cjm571/diyer-cutter/docs/KiCad/DIYer_Cutter/DIYer_Cutter.kicad_pcb

## KiCad design sch/Z80proto2/Comm_Module.kicad_sch

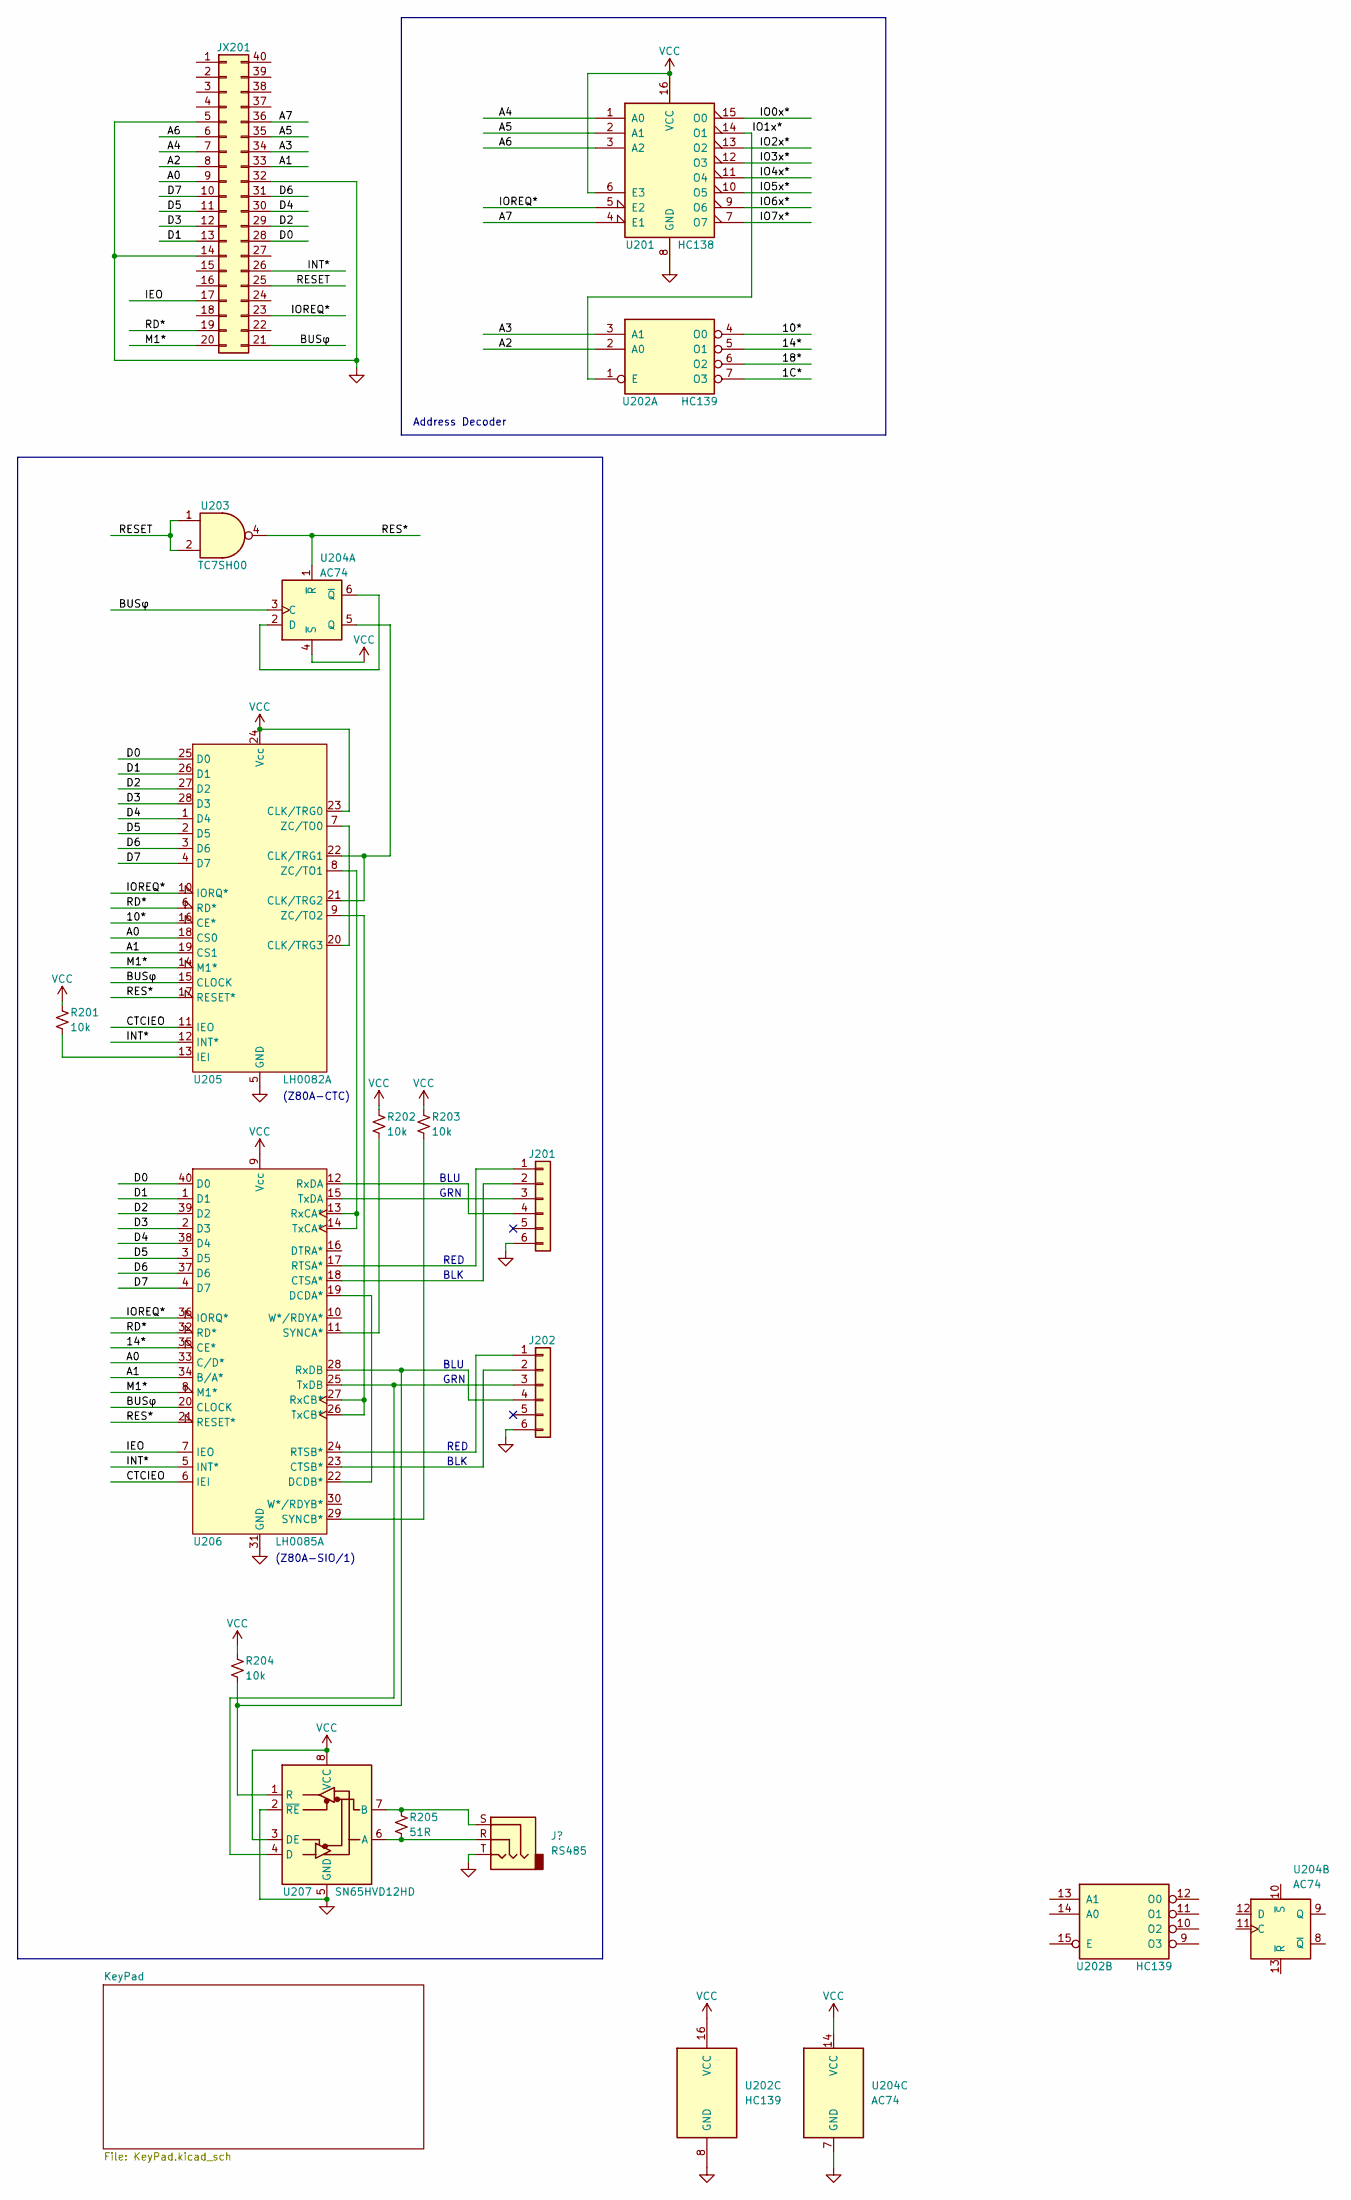
[picture p6: schematic Comm_Module.kicad_sch]

Parts:
J201, J202: Conn_01x06
JX201: Conn_02x20_Counter_Clockwise
R201, R202, R203, R204: 10k
R205: 51R
U201: HC138
U202: HC139
U203: TC7SH00
U204: AC74
U205: LH0082A
U206: LH0085A
U207: SN65HVD12HD; SOIC-8_3.9x4.9mm_P1.27mm

Connections:
1C*: U202.7 (O3)
10*: U202.4 (O0), U205.16 (CE*)
14*: U202.5 (O1), U206.35 (CE*)
18*: U202.6 (O2)
A0: JX201.9, U205.18 (CS0), U206.33 (C/D*)
A1: JX201.33, U205.19 (CS1), U206.34 (B/A*)
A2: JX201.8, U202.2 (A0)
A3: JX201.34, U202.3 (A1)
A4: JX201.7, U201.1 (A0)
A5: JX201.35, U201.2 (A1)
A6: JX201.6, U201.3 (A2)
A7: JX201.36, U201.4 (E1)
BUSφ: JX201.21, U204.3 (C), U205.15 (CLOCK), U206.20 (CLOCK)
CTCIEO: U205.11 (IEO), U206.6 (IEI)
D0: JX201.28, U205.25 (D0), U206.40 (D0)
D1: JX201.13, U205.26 (D1), U206.1 (D1)
D2: JX201.29, U205.27 (D2), U206.39 (D2)
D3: JX201.12, U205.28 (D3), U206.2 (D3)
D4: JX201.30, U205.1 (D4), U206.38 (D4)
D5: JX201.11, U205.2 (D5), U206.3 (D5)
D6: JX201.31, U205.3 (D6), U206.37 (D6)
D7: JX201.10, U205.4 (D7), U206.4 (D7)
IEO: JX201.17, U206.7 (IEO)
INT*: JX201.26, U205.12 (INT*), U206.5 (INT*)
IO0x*: U201.15 (O0)
IO1x*: U201.14 (O1), U202.1 (E)
IO2x*: U201.13 (O2)
IO3x*: U201.12 (O3)
IO4x*: U201.11 (O4)
IO5x*: U201.10 (O5)
IO6x*: U201.9 (O6)
IO7x*: U201.7 (O7)
IOREQ*: JX201.23, U201.5 (E2), U205.10 (IORQ*), U206.36 (IORQ*)
M1*: JX201.20, U205.14 (M1*), U206.8 (M1*)
unnamed: J201.1, U206.17 (RTSA*)
unnamed: J201.2, U206.18 (CTSA*)
unnamed: J201.3, U206.15 (TxDA)
unnamed: J201.4, U206.12 (RxDA)
unnamed: J202.1, U206.24 (RTSB*)
unnamed: J202.2, U206.23 (CTSB*)
unnamed: J202.3, U206.25 (TxDB), U207.4 (D)
unnamed: J202.4, R204.2, U206.28 (RxDB), U207.1 (R)
unnamed: JX201.5, JX201.14, JX201.32
unnamed: R201.2, U205.13 (IEI)
unnamed: R202.2, U206.11 (SYNCA*)
unnamed: R203.2, U206.29 (SYNCB*)
unnamed: R205.1, U207.7 (B)
unnamed: R205.2, U207.6 (A)
unnamed: U201.6 (E3), U201.16 (VCC)
unnamed: U204.2 (D), U204.6 (~Q)
unnamed: U204.5 (Q), U205.21 (CLK/TRG2), U205.22 (CLK/TRG1)
unnamed: U205.8 (ZC/TO1), U206.13 (RxCA*), U206.14 (TxCA*)
unnamed: U205.9 (ZC/TO2), U206.26 (TxCB*), U206.27 (RxCB*)
unnamed: U205.7 (ZC/TO0), U205.20 (CLK/TRG3)
unnamed: U205.23 (CLK/TRG0), U205.24 (Vcc)
unnamed: U206.19 (DCDA*), U206.22 (DCDB*)
unnamed: U207.2 (~RE), U207.5 (GND)
unnamed: U207.3 (DE), U207.8 (VCC)
RD*: JX201.19, U205.6 (RD*), U206.32 (RD*)
RES*: U203.4, U204.1 (~R), U205.17 (RESET*), U206.21 (RESET*)
RESET: JX201.25, U203.1, U203.2

Notes on the sheet:
BLK
RED
Address Decoder
(Z80A-CTC)
BLU
GRN
(Z80A-SIO/1)
