cjm571/diyer-cutter/docs/KiCad/DIYer_Cutter/DIYer_Cutter.kicad_pcb

## KiCad design sch/Z80proto2/KeyPad.kicad_sch

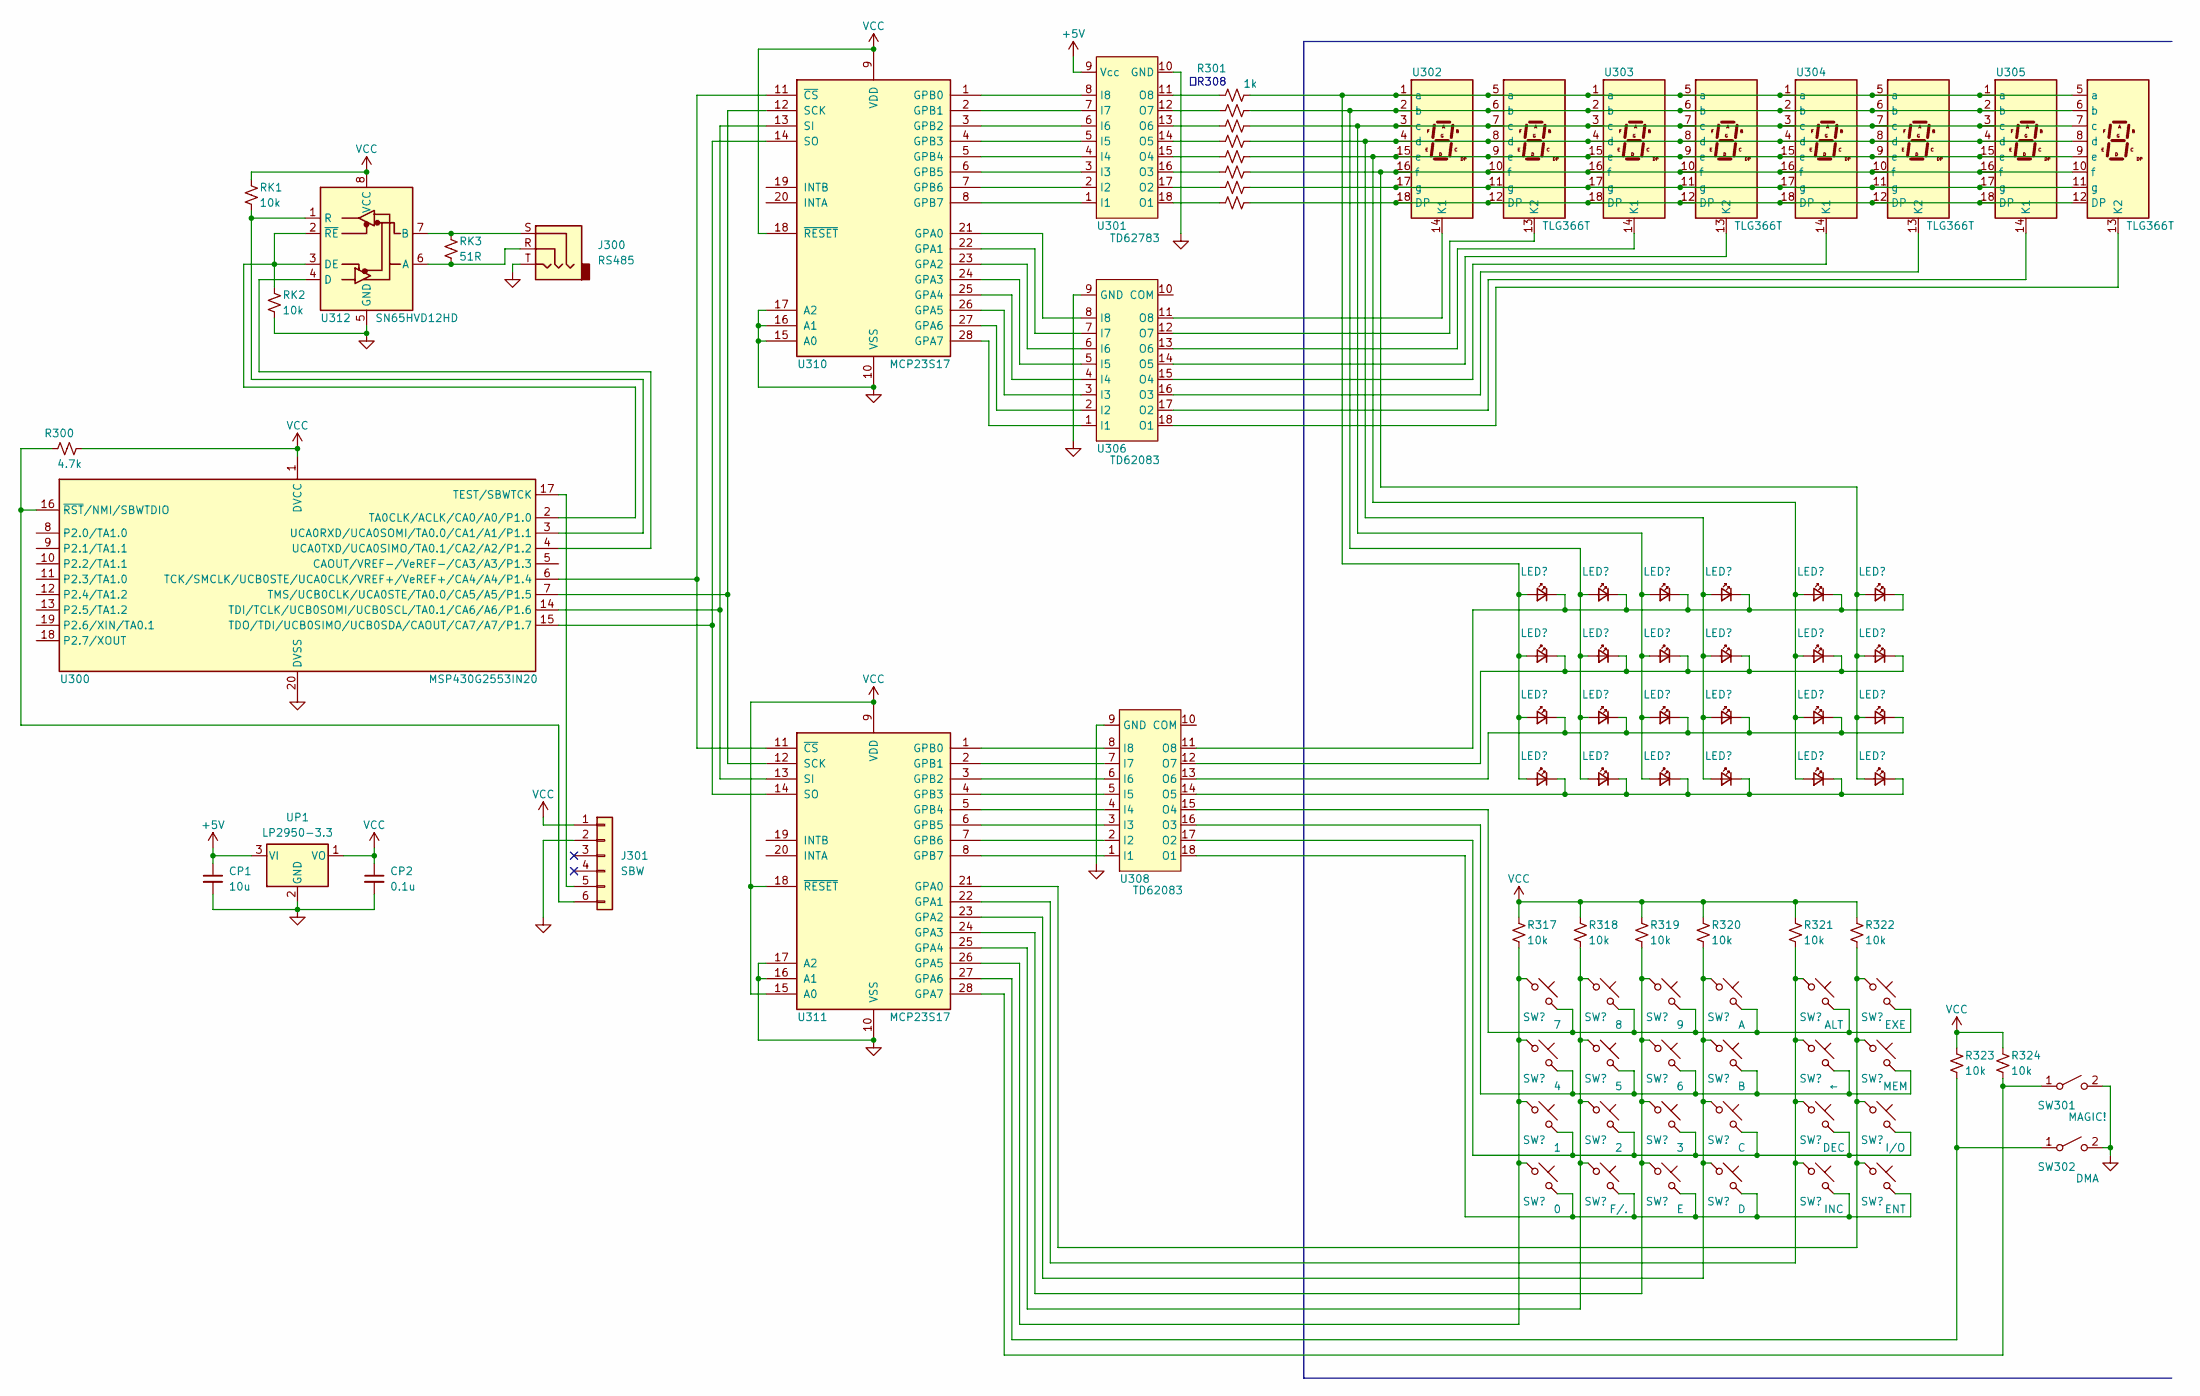
[picture p8: schematic KeyPad.kicad_sch]

Parts:
CP1: 10u
CP2: 0.1u
J300: RS485
J301: SBW
R300: 4.7k
R301, R302, R303, R304, R305, R306, R307, R308: 1k
R317, R318, R319, R320, R321, R322, R323, R324: 10k
RK1, RK2: 10k
RK3: 51R
SW301: MAGIC!
SW302: DMA
U300: MSP430G2553IN20; DIP-20_W7.62mm
U301: TD62783
U302, U303, U304, U305: TLG366T
U306, U308: TD62083
U310, U311: MCP23S17; DIP-28_W7.62mm
U312: SN65HVD12HD; SOIC-8_3.9x4.9mm_P1.27mm
UP1: LP2950-3.3; TO-92_Inline

Connections:
unnamed: CP1.1, UP1.3 (VI)
unnamed: CP1.2, CP2.2, UP1.2 (GND)
unnamed: CP2.1, UP1.1 (VO)
unnamed: J300.R, RK3.2, U312.6 (A)
unnamed: J300.S, RK3.1, U312.7 (B)
unnamed: J301.5, U300.17 (TEST/SBWTCK)
unnamed: J301.6, R300.1, U300.16 (~RST/NMI/SBWTDIO)
unnamed: R300.2, U300.1 (DVCC)
unnamed: R301.1, U301.11 (O8)
unnamed: R301.2, U302.1 (a), U302.5 (a), U303.1 (a), U303.5 (a), U304.1 (a), U304.5 (a), U305.1 (a), U305.5 (a)
unnamed: R302.1, U301.12 (O7)
unnamed: R302.2, U302.2 (b), U302.6 (b), U303.2 (b), U303.6 (b), U304.2 (b), U304.6 (b), U305.2 (b), U305.6 (b)
unnamed: R303.1, U301.13 (O6)
unnamed: R303.2, U302.3 (c), U302.7 (c), U303.3 (c), U303.7 (c), U304.3 (c), U304.7 (c), U305.3 (c), U305.7 (c)
unnamed: R304.1, U301.14 (O5)
unnamed: R304.2, U302.4 (d), U302.8 (d), U303.4 (d), U303.8 (d), U304.4 (d), U304.8 (d), U305.4 (d), U305.8 (d)
unnamed: R305.1, U301.15 (O4)
unnamed: R305.2, U302.9 (e), U302.15 (e), U303.9 (e), U303.15 (e), U304.9 (e), U304.15 (e), U305.9 (e), U305.15 (e)
unnamed: R306.1, U301.16 (O3)
unnamed: R306.2, U302.10 (f), U302.16 (f), U303.10 (f), U303.16 (f), U304.10 (f), U304.16 (f), U305.10 (f), U305.16 (f)
unnamed: R307.1, U301.17 (O2)
unnamed: R307.2, U302.11 (g), U302.17 (g), U303.11 (g), U303.17 (g), U304.11 (g), U304.17 (g), U305.11 (g), U305.17 (g)
unnamed: R308.1, U301.18 (O1)
unnamed: R308.2, U302.12 (DP), U302.18 (DP), U303.12 (DP), U303.18 (DP), U304.12 (DP), U304.18 (DP), U305.12 (DP), U305.18 (DP)
unnamed: R317.1, R318.1, R319.1, R320.1, R321.1, R322.1
unnamed: R317.2, U311.26 (GPA5)
unnamed: R318.2, U311.25 (GPA4)
unnamed: R319.2, U311.24 (GPA3)
unnamed: R320.2, U311.23 (GPA2)
unnamed: R321.2, U311.22 (GPA1)
unnamed: R322.2, U311.21 (GPA0)
unnamed: R323.1, R324.1
unnamed: R323.2, SW302.1 (A), U311.27 (GPA6)
unnamed: R324.2, SW301.1 (A), U311.28 (GPA7)
unnamed: RK1.1, U312.8 (VCC)
unnamed: RK1.2, U300.3 (UCA0RXD/UCA0SOMI/TA0.0/CA1/A1/P1.1), U312.1 (R)
unnamed: RK2.1, U300.2 (TA0CLK/ACLK/CA0/A0/P1.0), U312.2 (~RE), U312.3 (DE)
unnamed: RK2.2, U312.5 (GND)
unnamed: SW301.2 (B), SW302.2 (B)
unnamed: U300.4 (UCA0TXD/UCA0SIMO/TA0.1/CA2/A2/P1.2), U312.4 (D)
unnamed: U300.6 (TCK/SMCLK/UCB0STE/UCA0CLK/VREF+/VeREF+/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), U310.11 (~CS), U311.11 (~CS)
unnamed: U300.7 (TMS/UCB0CLK/UCA0STE/TA0.0/CA5/A5/P1.5), U310.12 (SCK), U311.12 (SCK)
unnamed: U300.14 (TDI/TCLK/UCB0SOMI/UCB0SCL/TA0.1/CA6/A6/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), U310.13 (SI), U311.13 (SI)
unnamed: U300.15 (TDO/TDI/UCB0SIMO/UCB0SDA/CAOUT/CA7/A7/P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), U310.14 (SO), U311.14 (SO)
unnamed: U301.1 (I1), U310.8 (GPB7)
unnamed: U301.2 (I2), U310.7 (GPB6)
unnamed: U301.3 (I3), U310.6 (GPB5)
unnamed: U301.4 (I4), U310.5 (GPB4)
unnamed: U301.5 (I5), U310.4 (GPB3)
unnamed: U301.6 (I6), U310.3 (GPB2)
unnamed: U301.7 (I7), U310.2 (GPB1)
unnamed: U301.8 (I8), U310.1 (GPB0)
unnamed: U302.13 (K2), U306.12 (O7)
unnamed: U302.14 (K1), U306.11 (O8)
unnamed: U303.13 (K2), U306.14 (O5)
unnamed: U303.14 (K1), U306.13 (O6)
unnamed: U304.13 (K2), U306.16 (O3)
unnamed: U304.14 (K1), U306.15 (O4)
unnamed: U305.13 (K2), U306.18 (O1)
unnamed: U305.14 (K1), U306.17 (O2)
unnamed: U306.1 (I1), U310.28 (GPA7)
unnamed: U306.2 (I2), U310.27 (GPA6)
unnamed: U306.3 (I3), U310.26 (GPA5)
unnamed: U306.4 (I4), U310.25 (GPA4)
unnamed: U306.5 (I5), U310.24 (GPA3)
unnamed: U306.6 (I6), U310.23 (GPA2)
unnamed: U306.7 (I7), U310.22 (GPA1)
unnamed: U306.8 (I8), U310.21 (GPA0)
unnamed: U308.1 (I1), U311.8 (GPB7)
unnamed: U308.2 (I2), U311.7 (GPB6)
unnamed: U308.3 (I3), U311.6 (GPB5)
unnamed: U308.4 (I4), U311.5 (GPB4)
unnamed: U308.5 (I5), U311.4 (GPB3)
unnamed: U308.6 (I6), U311.3 (GPB2)
unnamed: U308.7 (I7), U311.2 (GPB1)
unnamed: U308.8 (I8), U311.1 (GPB0)
unnamed: U310.10 (VSS), U310.15 (A0), U310.16 (A1), U310.17 (A2)
unnamed: U310.9 (VDD), U310.18 (~RESET)
unnamed: U311.10 (VSS), U311.16 (A1), U311.17 (A2)
unnamed: U311.9 (VDD), U311.15 (A0), U311.18 (~RESET)

Notes on the sheet:
～R308
